shannon-greenlight/twangilizer/docs/spice/vactrol_test_rig.asc

D1: LED
D2: LED
D3: LED
D4: LED
R1: res; 20K
R2: res; 523
R3: res; 395
R4: res; 523
R5: res; 900
R6: res; 10K
R7: res; 523
R8: res; 400
R9: res; 10K
U1: LT1354
U2: LT1354
U3: LT1354
V1: voltage; 12
V2: voltage; 12
V3: voltage; 5
Named nets: 0, +12, -12, Bias, Vtest, HiRef, LoRef
;.dc V3 0 10 .01
;tran 0 1 0 .1
.op
Too High
Too Low
DUT
DUT
LED Good
