shannon-greenlight/twangilizer/docs/spice/clip_detector.asc

C1: cap; .1µF
C3: cap; 47pF
D1: schottky; 1N5817
D2: LED
D3: schottky; 1N5817
D4: diode; 1N4148
D5: diode; 1N4148
R1: res; 10K
R2: res; 5.6K
R3: res; 1Meg
R4: res; 100K
R5: res; 10K
R6: res; 10K
R7: res; 11K
R8: res; 10K
R9: res; 10K
U1: LT1354
U2: LT1354
U3: LT1017
U4: LT1354
V1: voltage; 11.5
V2: voltage; 11.6
V3: voltage; 9
V4: voltage; 9
V5: voltage; SINE(0 9.3 20)
Named nets: 0, +12, -12, +9, -9, SigIn, RectOut
.tran 0 1.5 .15
