shannon-greenlight/twangilizer/docs/spice/clip_detector2.asc

C3: cap; 47pF
D1: zener; PTZ8_2B
D2: LED
D4: diode; 1N4148
D5: diode; 1N4148
R1: res; 10K
R2: res; 100
R5: res; 10K
R6: res; 10K
U1: LT1354
U4: LT1354
V1: voltage; 11.5
V2: voltage; 11.6
V3: voltage; 9
V4: voltage; 9
V5: voltage; SINE(0 10 2000 0 0 0)
Named nets: 0, +12, -12, +9, -9, SigIn
.tran 0 .1025 .1
