shannon-greenlight/twangilizer/docs/spice/Draft1.asc

D1: LED; NSCW100
D2: diode; 1N4148
Q1: npn; 2N3904
R1: res; 100K
R2: res; 50K
R3: res; 200
V1: voltage; 9
V2: voltage; SINE(0 1 1000)
Named nets: 0, 9V
;op
.tran 0 5e-3 1e-3
