shannon-greenlight/twangilizer/docs/spice/pll_loop_filt_1.asc

C1: cap; 10µF
R1: res; 1.5K
R2: res; 27K
V1: voltage; SINE(0 1 20 0 0 0); AC 1
Named nets: 0
;.tran 0 2 1.9
.ac dec 10 .1 1000
