shannon-greenlight/twangilizer/docs/spice/pll_loop_filt_2.asc

C1: cap; 4.7µF
R1: res; 2.2K
R2: res; 30K
V1: voltage; SINE(0 1 20 0 0 0); AC 1
Named nets: 0
;.tran 0 2 1.9
.ac dec 10 1 10000
