shannon-greenlight/twangilizer/docs/spice/pll_loop_filt_active.asc

C1: cap; 160nF
C2: cap; 1.1µF
C3: cap; 3.9µF
R1: res; 2K
R2: res; 24.3K
R3: res; 14.3K
R8: res; 50K
R9: res; 950K
U1: LT1354
U2: LT1354
V1: voltage; 11.5
V2: voltage; 11.6
V3: voltage; 9
V4: voltage; 9
V5: voltage; SINE(0 1 20); AC 1
Named nets: 0, +12, -12, +9, -9, SigIn, Out1, Out2
;tran 0 1.5 .15
.ac dec 10 1 1000
