shannon-greenlight/twangilizer/docs/spice/pll_loop_filt_active2.asc

C1: cap; 160nF
C2: cap; 4.7µF
C3: cap; 4.7µF
R1: res; 7.5K
R2: res; 20K
R3: res; 10K
R8: res; 50K
R9: res; 950K
U1: LT1354
U2: LT1354
V1: voltage; 11.5
V2: voltage; 11.6
V3: voltage; 9
V4: voltage; 9
V5: voltage; SINE(0 1 20); AC 1
Named nets: 0, +12, -12, +9, -9, SigIn, Out1, Out2
;tran 0 1.5 .15
.ac dec 10 1 100000
