shannon-greenlight/twangilizer/docs/spice/CLK Pickoff.asc

C1: cap; 220nF
C2: cap; 330pF
D1: diode
D2: LED
Q1: npn
Q2: pnp
R1: res; 2K
R2: res; 100K
R3: res; 5.1K
R4: res; 100K
R5: res; 10K
R6: res; 200K
R7: res; 68K
R8: res; 2K
R9: res; 68K
R10: res; 1K
R11: res; 100K
R14: res; 8.87K
R15: res; 10.0K
U1: OP27
U2: OP27
U3: LT1356
V1: voltage; 12
V2: voltage; 12
V3: voltage; PULSE(0 .05 0 1e-6 1e-6 50e-6 100e-6); AC 1
V4: voltage; 9
V5: voltage; 9
V6: voltage; .01
Named nets: 0, +12, -12, +9V, -9V
;tran 0 200e-6 0
.ac oct 20 1 2e5
Positive bias insures LED doesn't light
when no signal is present
