shannon-greenlight/twangilizer/docs/spice/final_output.asc

C1: cap; 2.7nF
C2: cap; 2nF
C3: cap; 2.7nF
C4: cap; 270pF
R1: res; 7.87K
R3: res; 16.5K
R4: res; 16.5K
R5: res; 59K
U1: LT1354
U2: LT1354
V1: voltage; 11.5
V2: voltage; 11.6
V3: voltage; SINE(2.0 1.5 .1 0.00001 0.00001 .1 .3); AC 1; Rser=0
Named nets: 0, +12, -12
;tran 0 1 0 .1
.ac dec 50 100 250e3
