shannon-greenlight/twangilizer/docs/spice/VCO Pickoff.asc

C1: cap; 47nF
C2: cap; 20nF
R1: res; 49.9K
R2: res; 1.12Meg
R3: res; 499K
R4: res; 2.65Meg
R5: res; 221K
R6: res; 1Meg
R7: res; 1Meg
R8: res; 2.61Meg
U1: LT1354
U2: LT1354
V1: voltage; 11.5
V2: voltage; 11.6
V3: voltage; PULSE(2 2.5 0 1e-5 1e-5 250e-6 10e-3); AC 1; Rser=0
V4: voltage; 9
Named nets: 0, +12, -12, -9V
;tran 0 50e-3 0 1e-3
Input: 1.0V - 9.0V
Output: -10V - 10.3V
Vo = Vp(1 + R2/R1)
Vp = [(Vi - -12V)/R3+R4]R4 + -12V
;dc V3 0 9 .1
.ac dec 25 1 1e4
;tran 0 1 0 .1
