shannon-greenlight/twangilizer/docs/spice/VCF model.asc

C1: cap; 1nF
C2: cap; 220pF
C3: cap; 24nF
C4: cap; 24nF
C5: cap; 100pF
C6: cap; 1nF
C7: cap; 6.8nF
C8: cap; 6.8nF
R1: res; 44.2K
R2: res; 1.96K
R3: res; 90.9K
R4: res; 2.05K
R5: res; 4.12K
R6: res; 10K
R7: res; 10K
R8: res; 121K
R9: res; 53.2K
R10: res; 30.1K
R11: res; 604
R12: res; 2.05K
R13: res; 2.15K
R14: res; 634
U1: LT1354
U2: LT1354
U3: LT1354
U4: LT1354
U5: LT1354
U6: LT1354
V1: voltage; 11.5
V2: voltage; 11.6
V3: voltage; PULSE(-1 1 0 1e-4 1e-4 .005 .01); AC 1; Rser=0
Named nets: 0, +12, -12, OSC, FILT, OUT
.ac oct 10 1e3 50e4
-3dB @9.2KHz
OSC -7.14dB
OSC +7.7dB
;tran 0 30e-3 0 .001
