shannon-greenlight/twangilizer/docs/spice/VCA.asc

D1: LED
D3: schottky; BAT54
D4: schottky; BAT54
R1: res; 20K
R2: res; 500
R3: res; 120K
R4: res; 210K
R5: res; 500
R6: res; 150K
R7: res; 59K
R8: res; 6K
U1: 4N25
U2: LT1354
V1: voltage; 11.5
V2: voltage; 11.6
V3: voltage; SINE(5 4 1 0.00001 0.00001); Rser=0
V4: voltage; 9
Named nets: 0, +12, -12, +9V, Vout
;tran 0 1 0 .1
.dc V3 0 10 .01
0 for 5V full scale
120K for 8V full scale
200K for 10V full scale
Simulates vactrol/op amp circuit
